bks008/audio_spectrum_visualizer/Main/Power.pdf

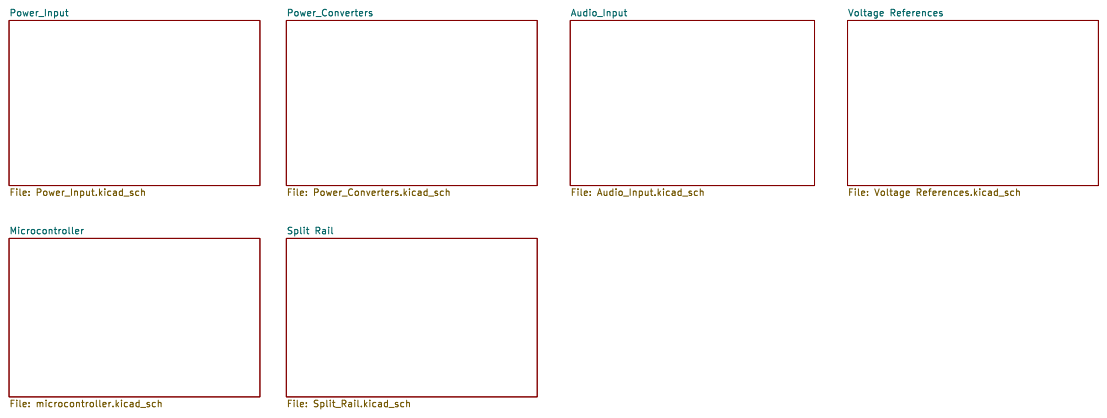
[picture p22: page 1]

Id: 1/7 Title: File: Power.kicad_sch Sheet: /

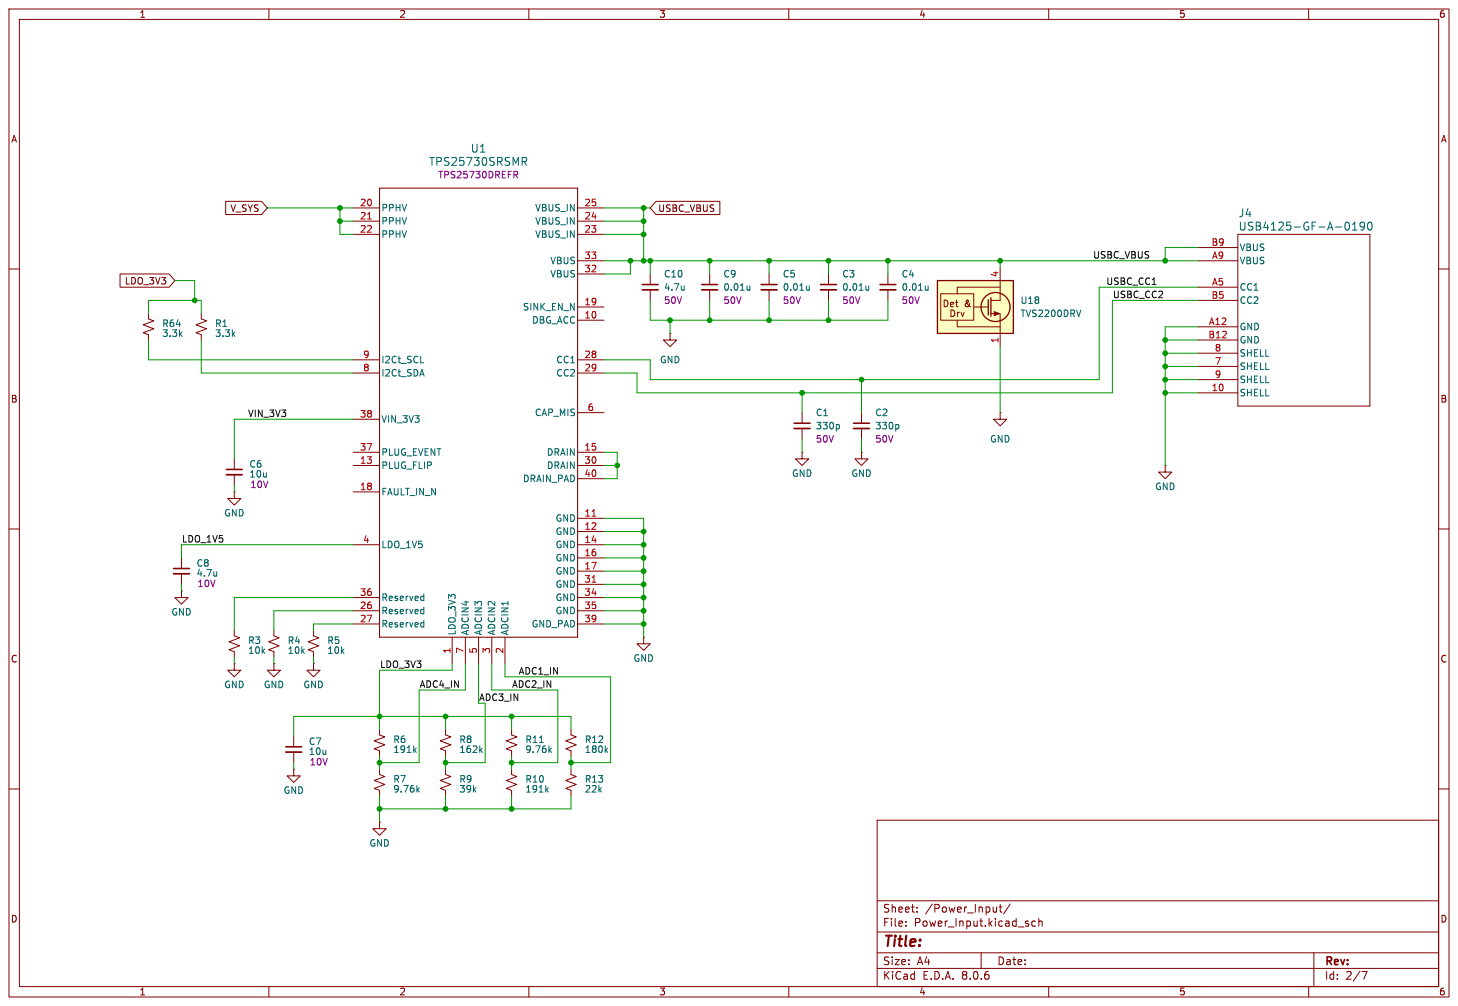
[picture p23: page 2]

2 PPHV 20 PPHV 21 PPHV 22 VBUS_IN 23 VBUS_IN 24 VBUS_IN 25 Reserved 26 Reserved 27 CC1 28 CC2 29 ADCIN2

3 DRAIN 30 GND 31 VBUS 32 VBUS 33 GND 34 GND 35 Reserved 36 PLUG_EVENT 37 VIN_3V3 38 GND_PAD 39

1 DBG_ACC 10 GND 11 GND 12 PLUG_FLIP 13 GND 14 DRAIN 15 GND 16 GND 17 FAULT_IN_N 18 SINK_EN_N 19 ADCIN1

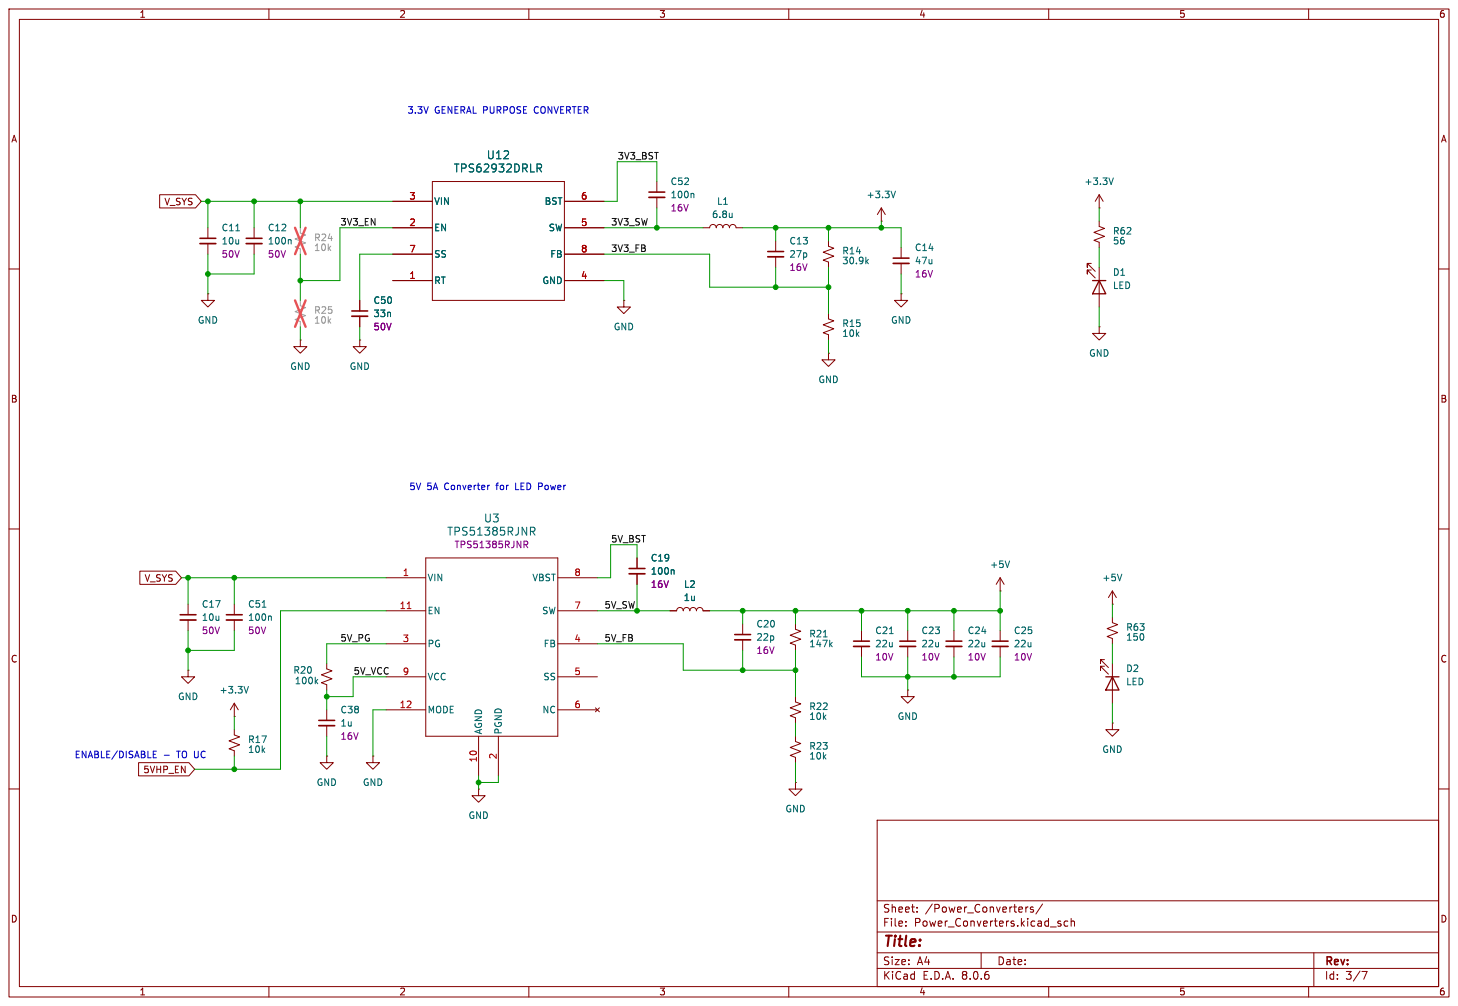
[picture p24: page 3]

5V 5A Converter for LED Power C50

2 PG 3 FB 4 SS 5 NC 6 SW 7 VBST 8 VCC 9 U3 TPS51385RJNR

Id: 3/7 Title: File: Power_Converters.kicad_sch Sheet: /Power_Converters/ C23

ENABLE/DISABLE - TO UC

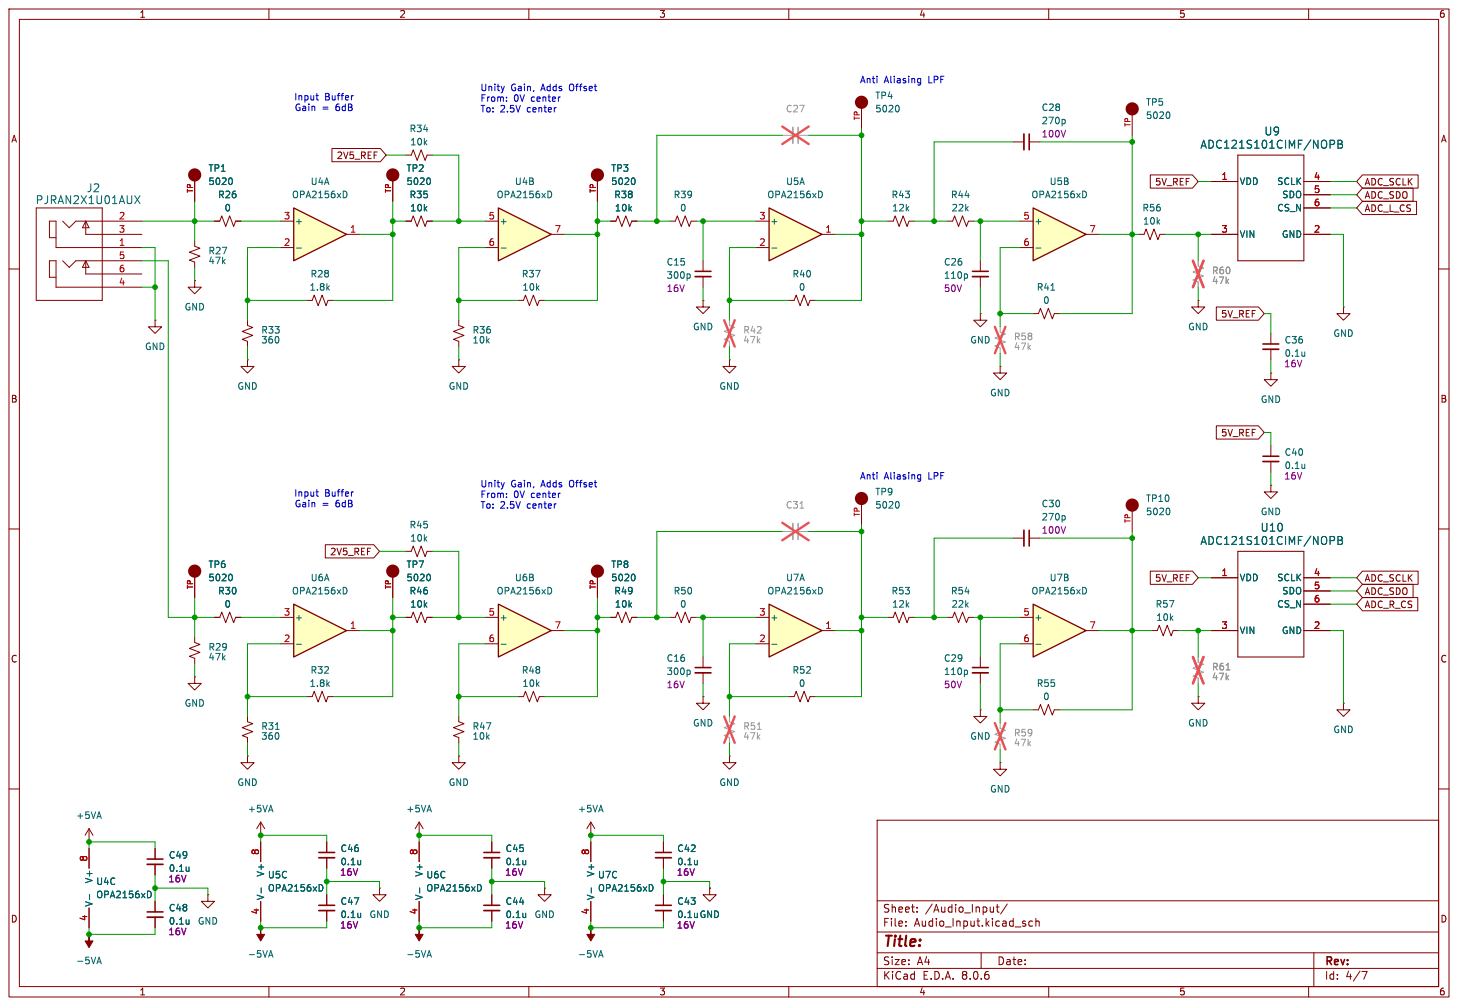
[picture p25: page 4]

Id: 4/7 Title: File: Audio_Input.kicad_sch Sheet: /Audio_Input/ R49

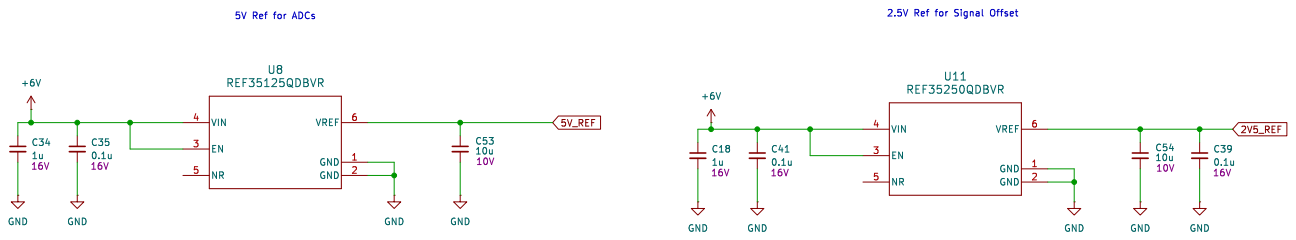
[picture p26: page 5]

2.5V Ref for Signal Offset 5V Ref for ADCs

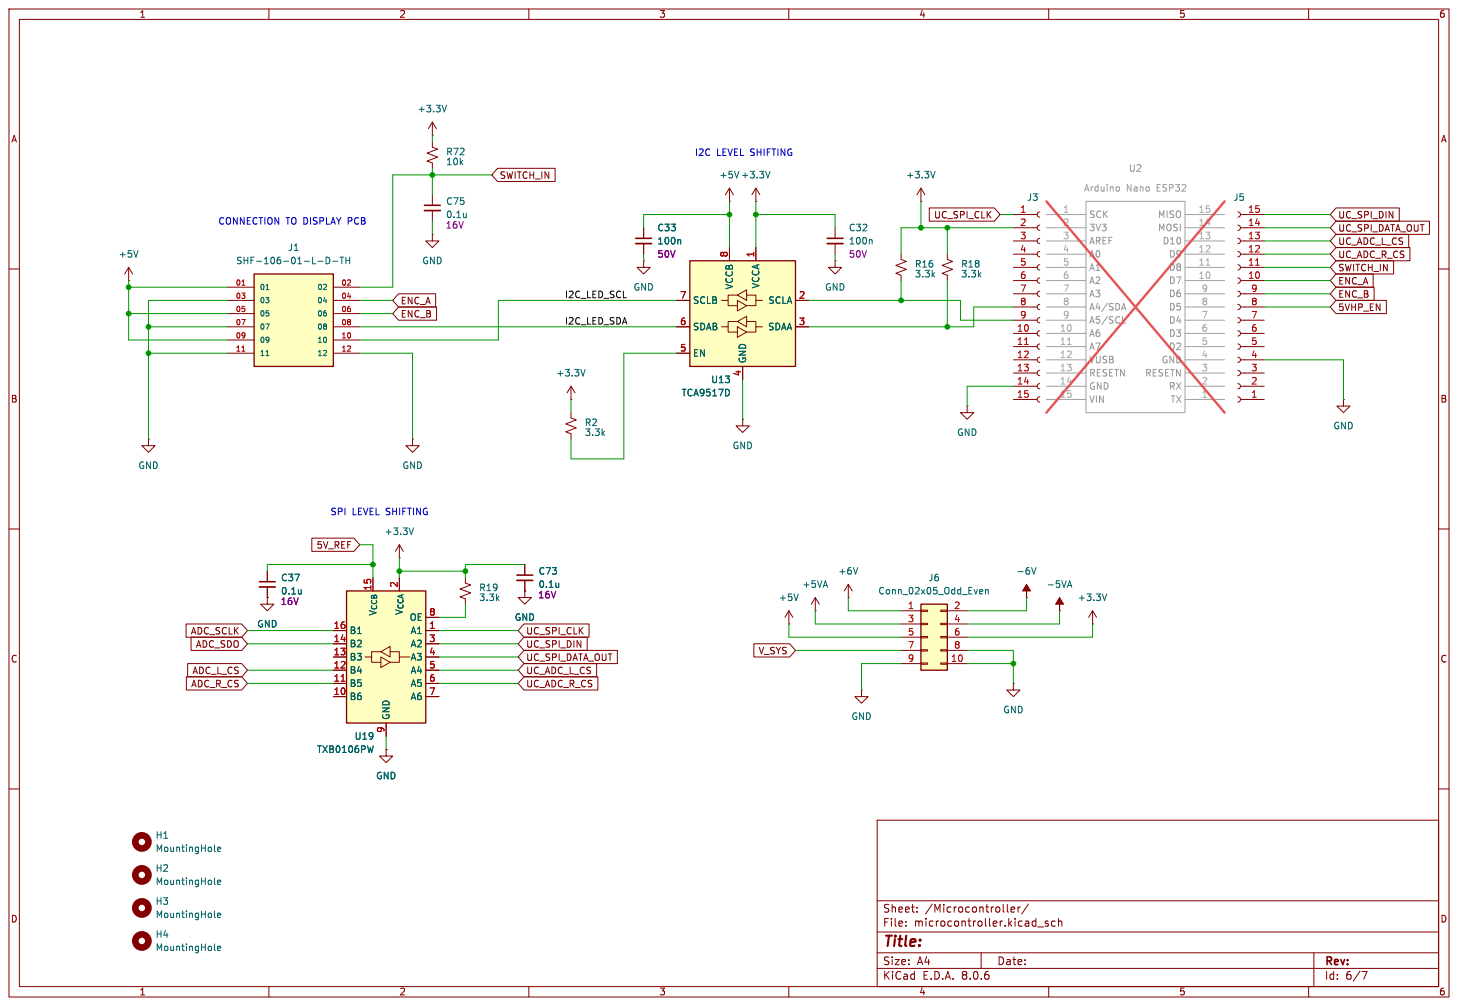
[picture p27: page 6]

8 U13 TCA9517D GND GND GND GND

4 EN 5 SDAB 6 SCLB 7 VCCB

Id: 6/7 Title: File: microcontroller.kicad_sch Sheet: /Microcontroller/ GND

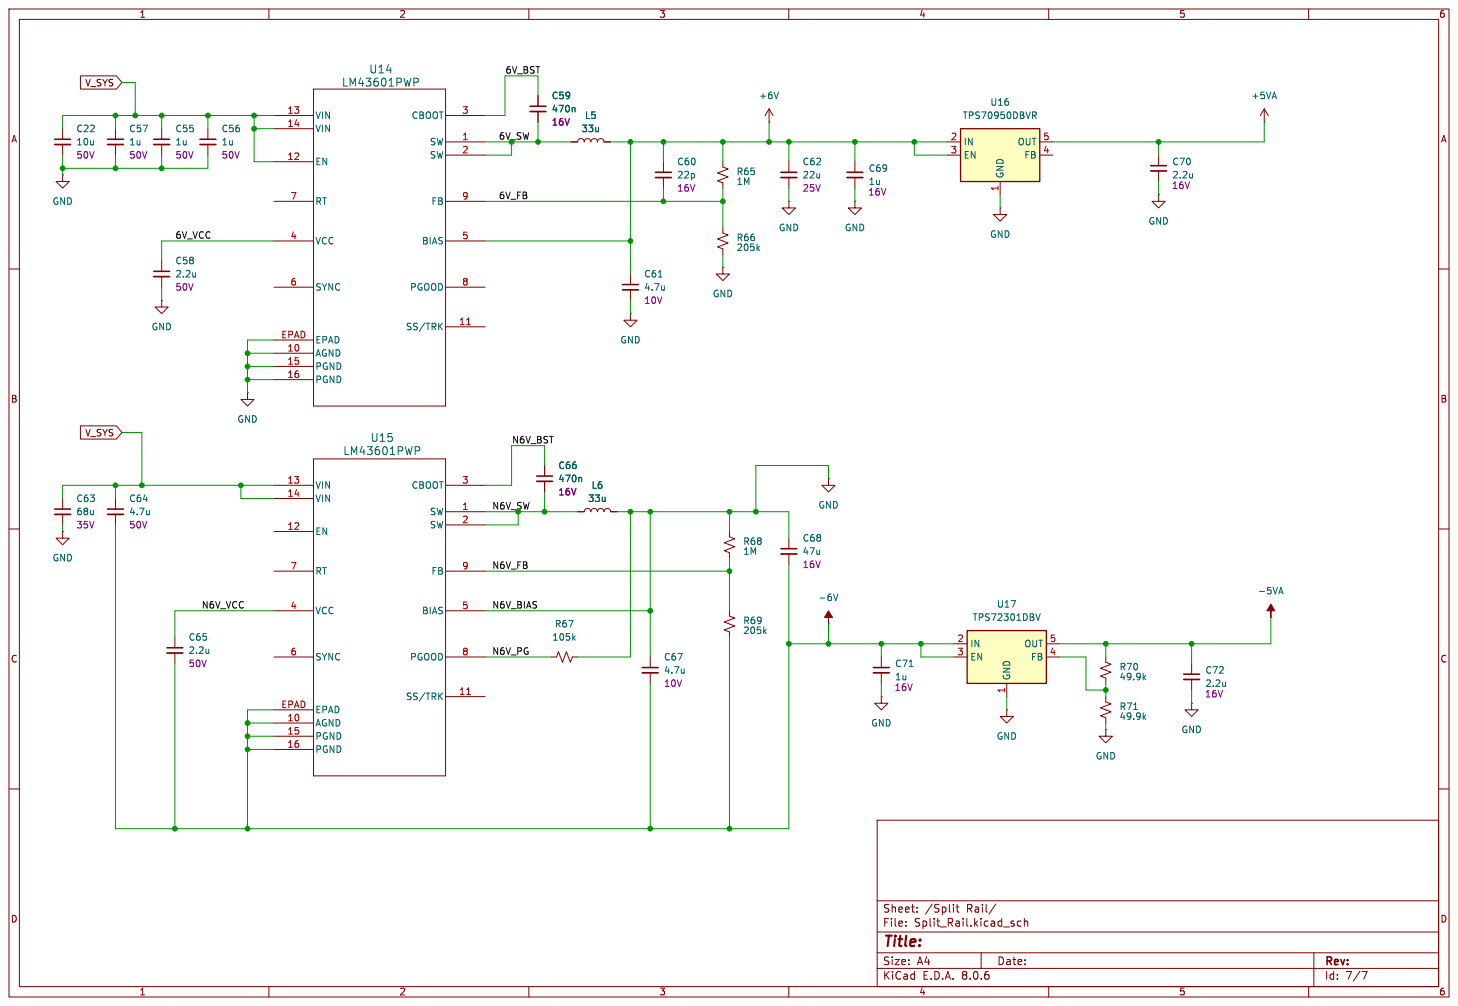
[picture p28: page 7]
