bks008/audio_spectrum_visualizer/Main/Layout_in2.pdf

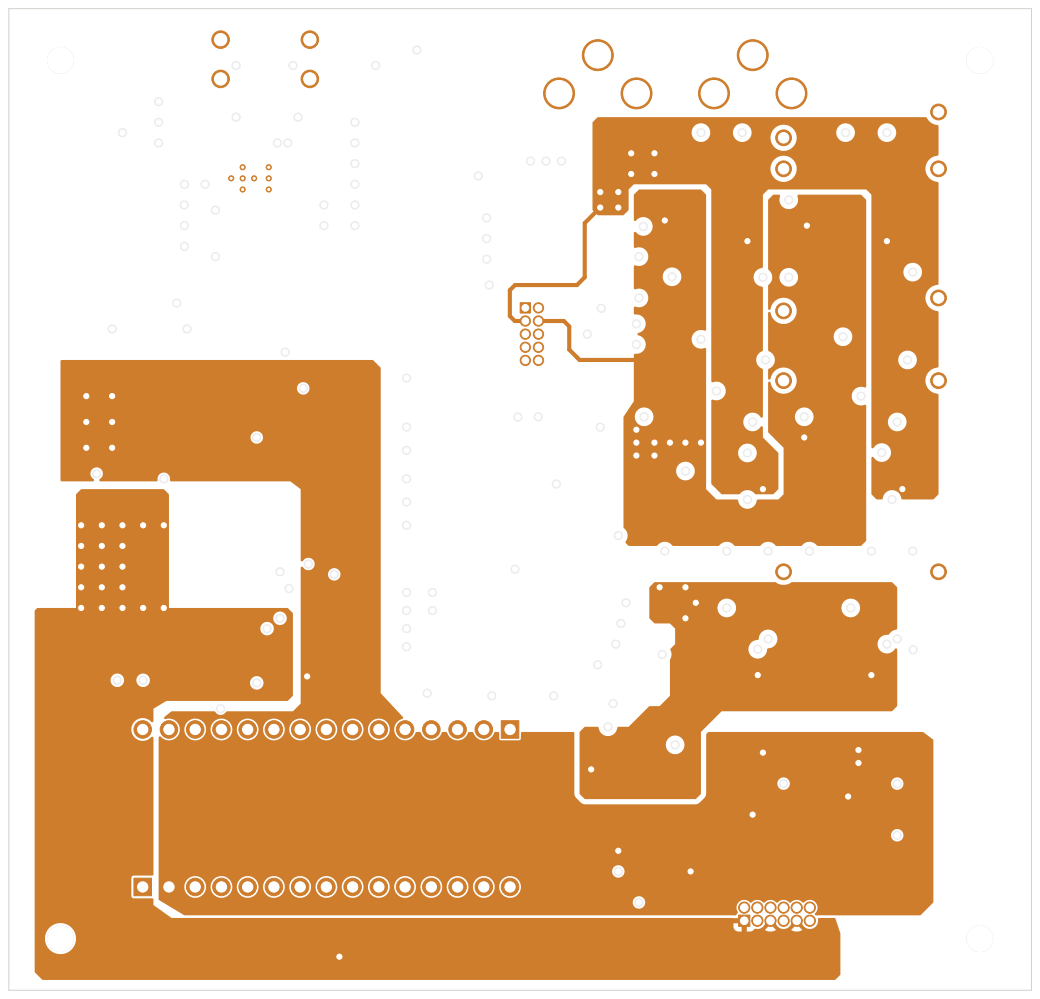
[picture p34: page 1]
