bks008/audio_spectrum_visualizer/Main/Analysis/opamp_sim/Draft1.asc

C1: cap; 300p
C3: cap; 110p
C4: cap; 270p
R1: res; 47k
R2: res; 360
R3: res; 10k
R4: res; 10k
R5: res; 10k
R6: res; 22k
R7: res; 10k
R8: res; 10k
R9: res; 0
R10: res; 12k
R11: res; 10k
R_fb: res; 1.8k
R_in: res; 0
U1: OPA2156
U2: OPA2156
U3: OPA2156
U4: OPA2156
V1: voltage; 5
V2: voltage; -5
V3: voltage; SINE(0 0.316 1k); AC 1
V-ref: voltage; 2.5
Named nets: 0, VCC, VEE
.ac oct 200 1 500k
Input Buffer
Gain = 6dB
Unity Gain, Adds Offset
From: 0V center
To: 2.5V center
.tran 10m
